lugsaar/ESP8266XmasTree/Graphics/di7jLG85T-523094331.jpeg

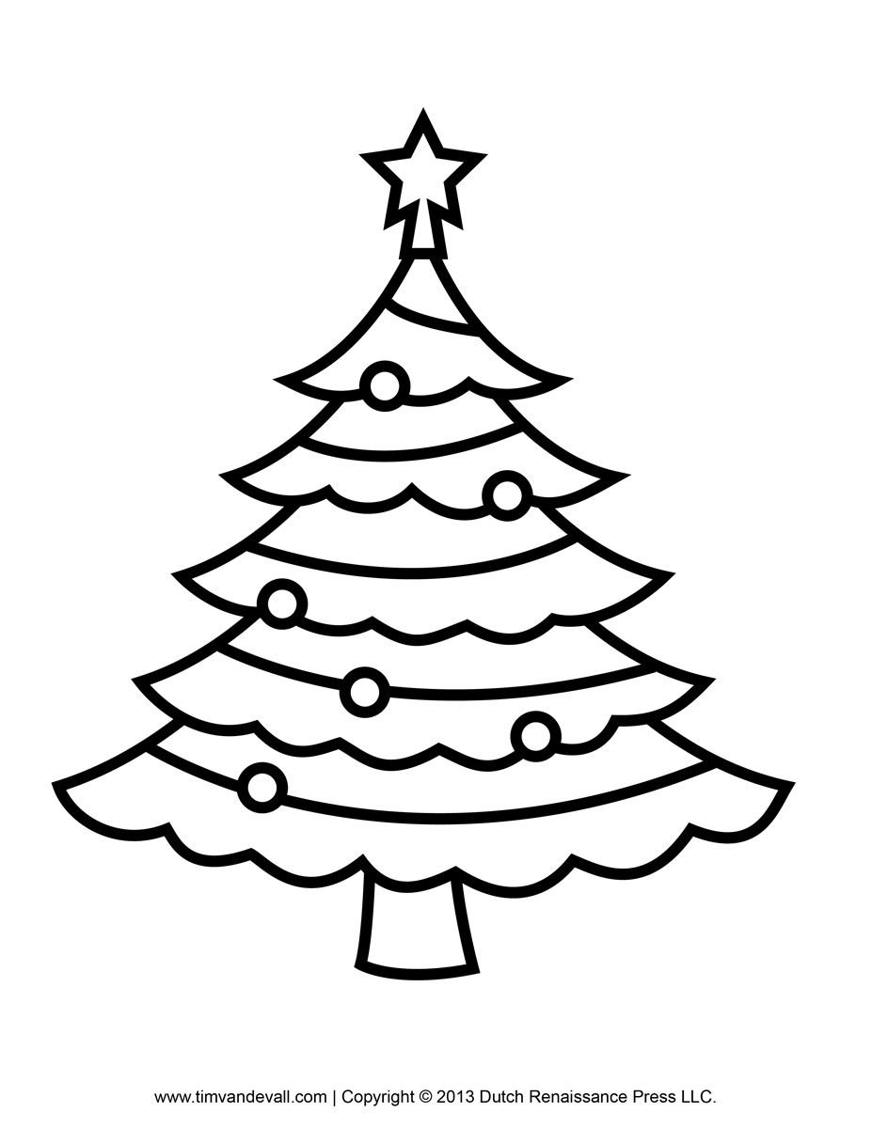
Graphics/di7jLG85T-523094331.jpeg
