lugsaar/ESP8266XmasTree/Graphics/gingerbreak_man.jpeg

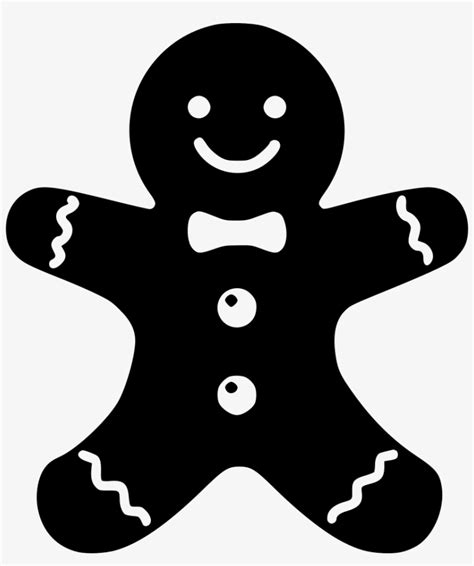
Graphics/gingerbreak_man.jpeg
