lugsaar/ESP8266XmasTree/Graphics/merry-christmas-text.jpeg

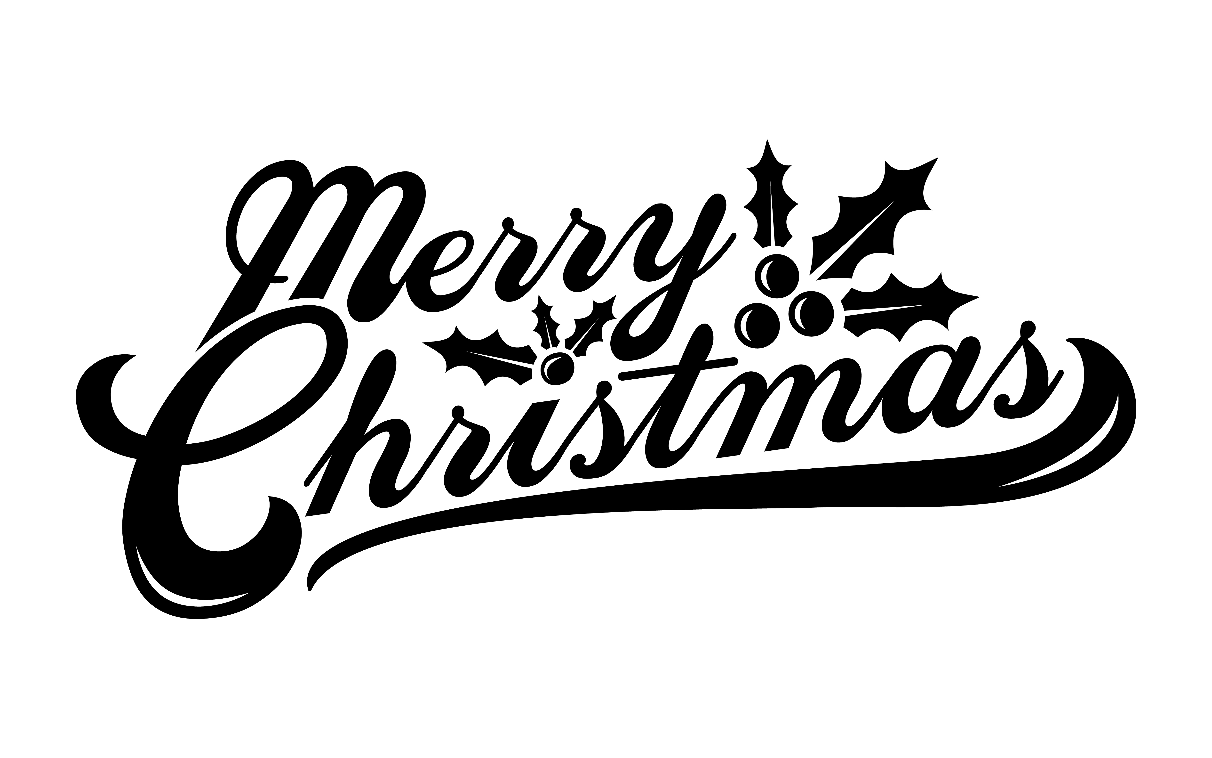
Graphics/merry-christmas-text.jpeg
