lugsaar/ESP8266XmasTree/Graphics/tux.png

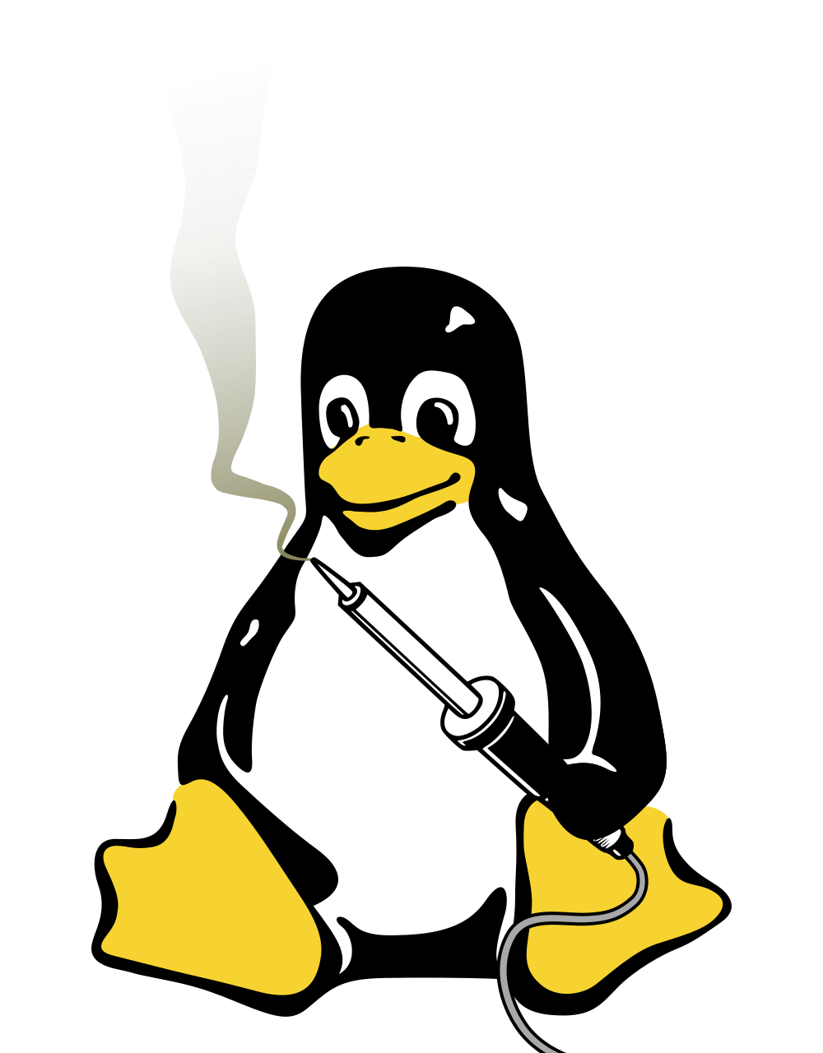
Graphics/tux.png
