lugsaar/ESP8266XmasTree/Graphics/Xmas_balls.png

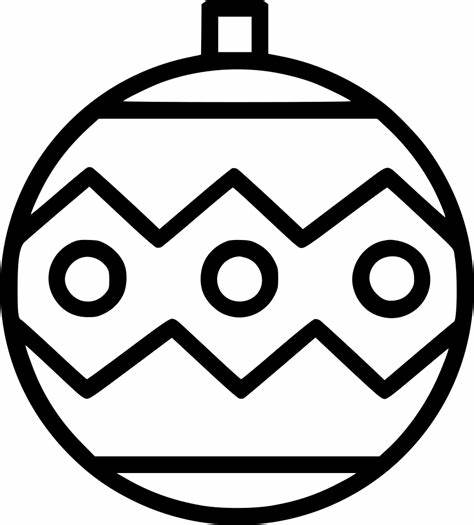
Graphics/Xmas_balls.png
