lugsaar/ESP8266XmasTree/Graphics/Xmas_present.png

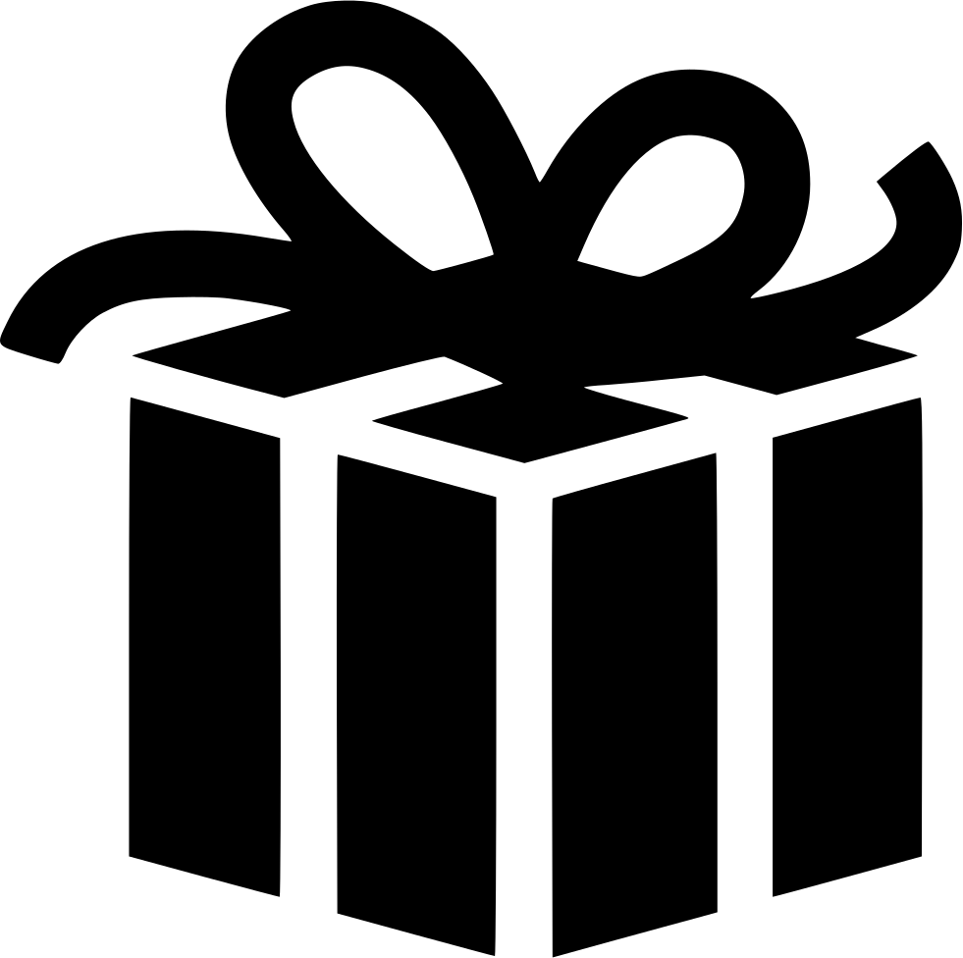
Graphics/Xmas_present.png
