lugsaar/ESP8266XmasTree/Graphics/Xmas_Snowman.png

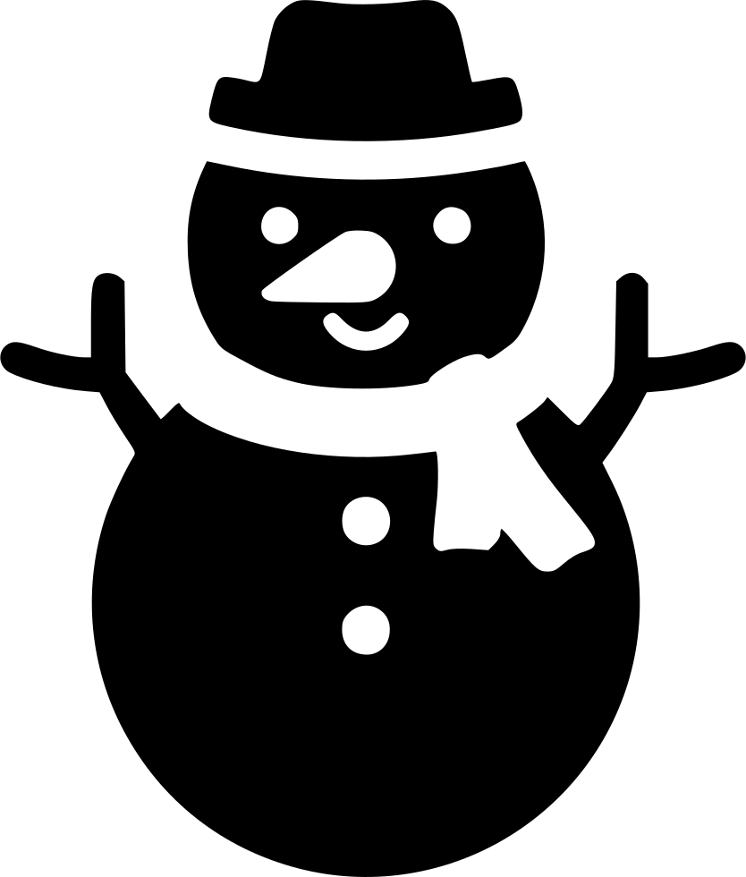
Graphics/Xmas_Snowman.png
